shikijaku/MSc-MIDI-Controller/pictures/IMG_9758.JPG

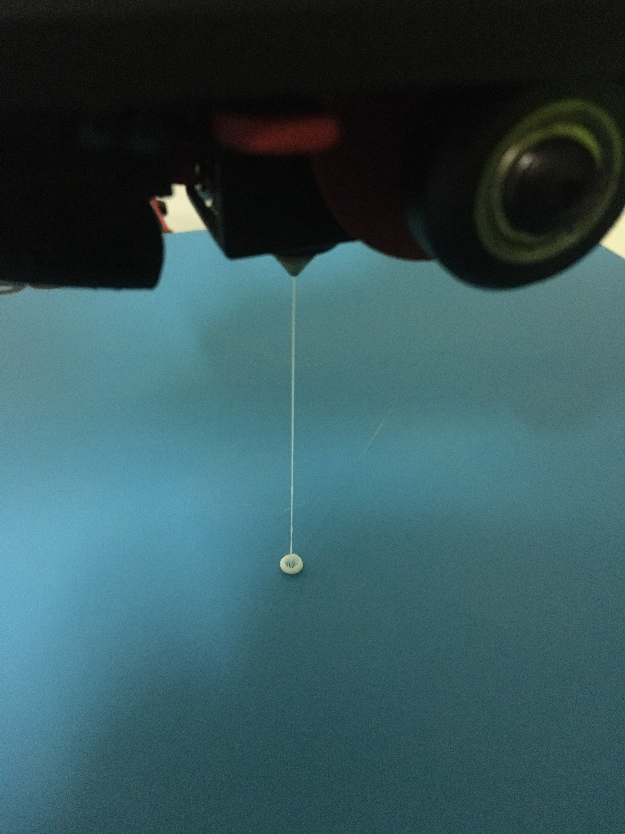
pictures/IMG_9758.JPG
