shikijaku/MSc-MIDI-Controller/pictures/IMG_9778.JPG

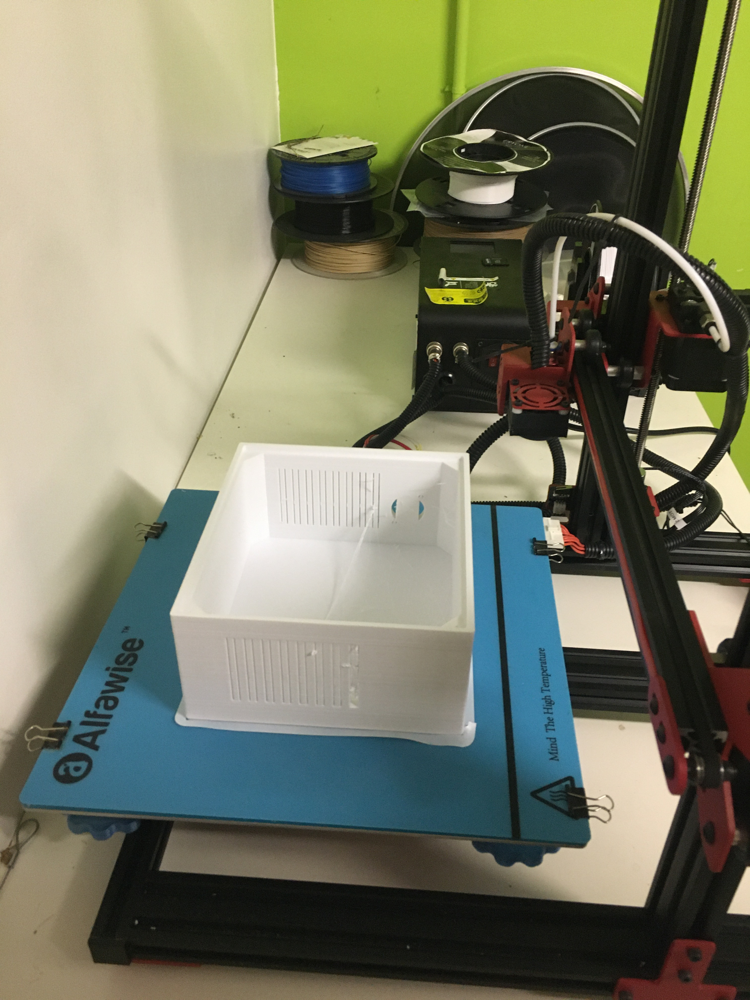
pictures/IMG_9778.JPG
