shikijaku/MSc-MIDI-Controller/pictures/IMG_9788.JPG

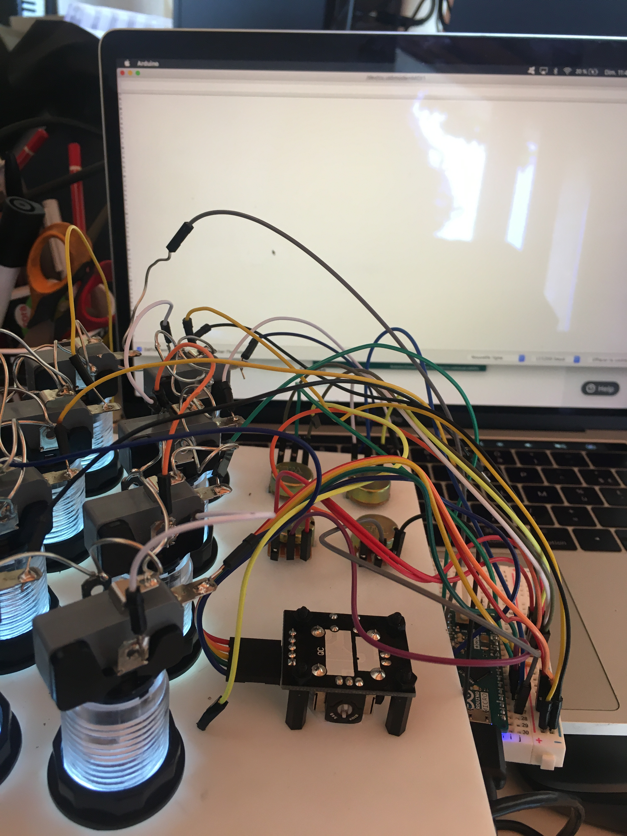
pictures/IMG_9788.JPG
