shikijaku/MSc-MIDI-Controller/pictures/IMG_9793.JPG

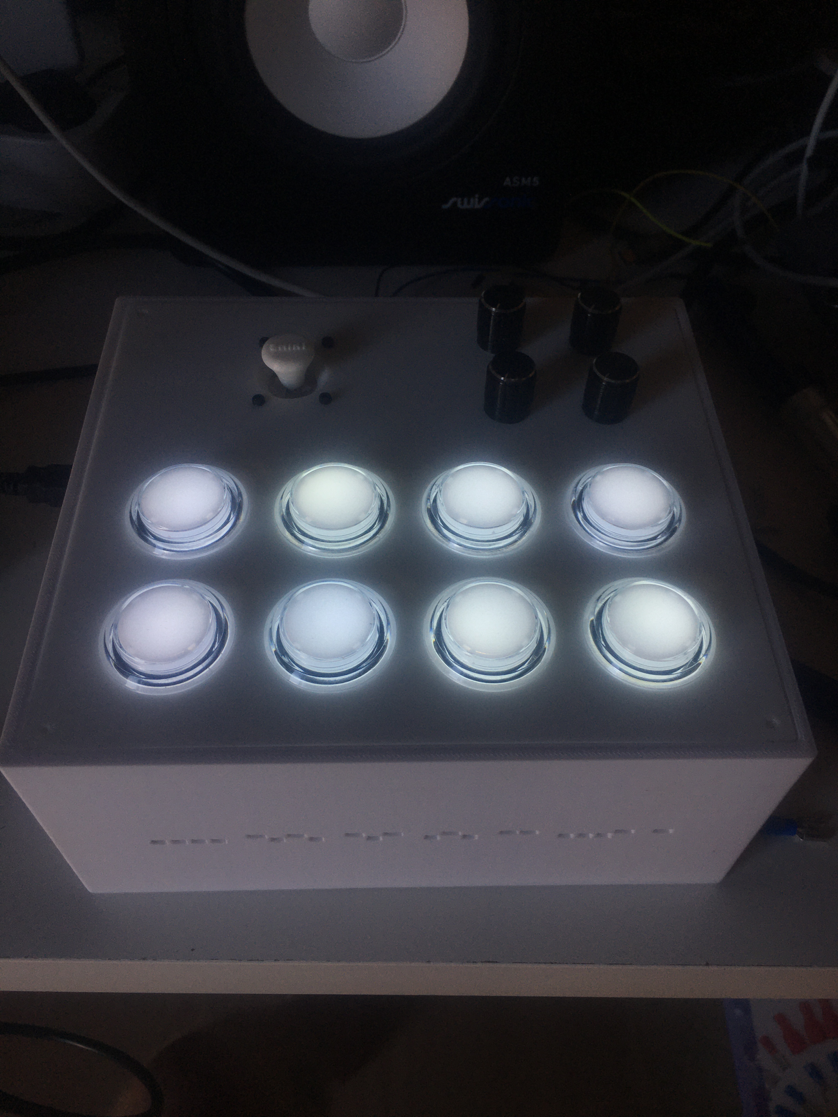
pictures/IMG_9793.JPG
