shikijaku/MSc-MIDI-Controller/pictures/IMG_9798.JPG

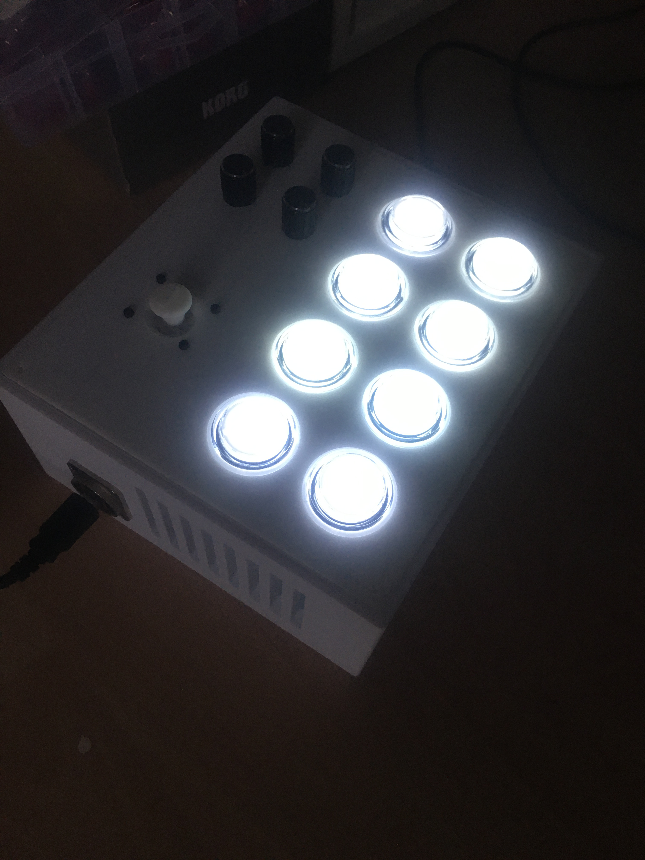
pictures/IMG_9798.JPG
