shikijaku/MSc-MIDI-Controller/pictures/IMG_9799.JPG

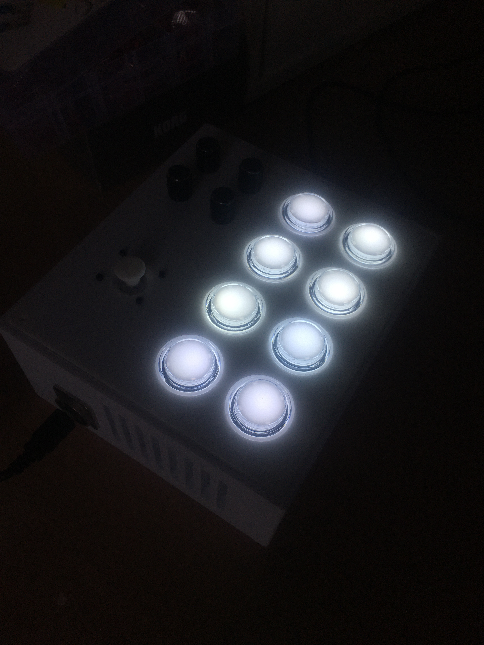
pictures/IMG_9799.JPG
