shikijaku/MSc-MIDI-Controller/pictures/IMG_9800.JPG

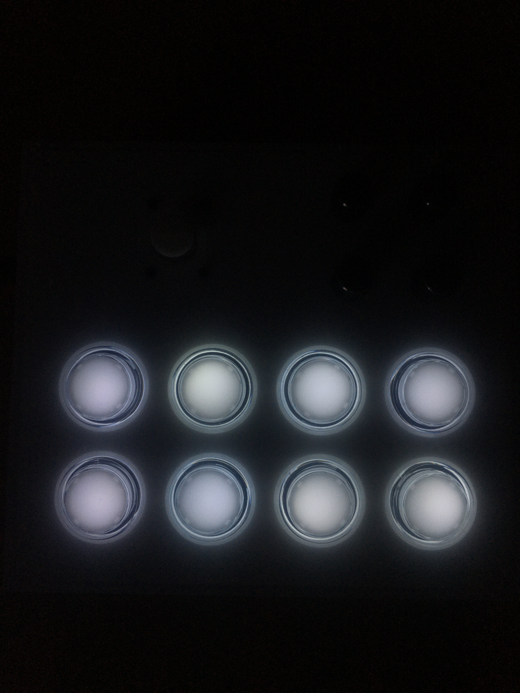
pictures/IMG_9800.JPG
