shikijaku/MSc-MIDI-Controller/pictures/IMG_9803.JPG

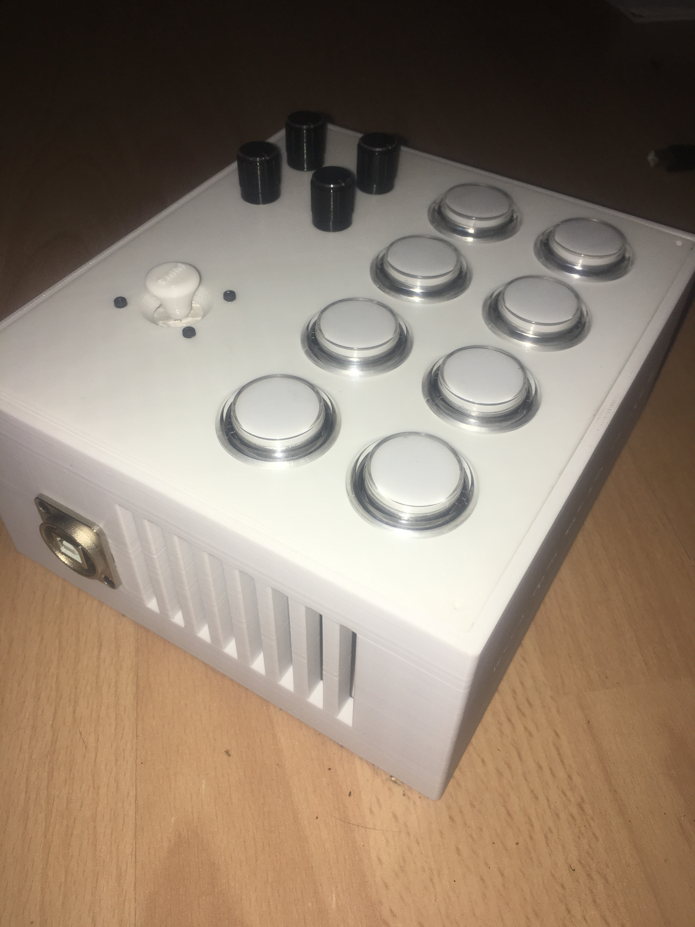
pictures/IMG_9803.JPG
