shikijaku/MSc-MIDI-Controller/pictures/IMG_9804.JPG

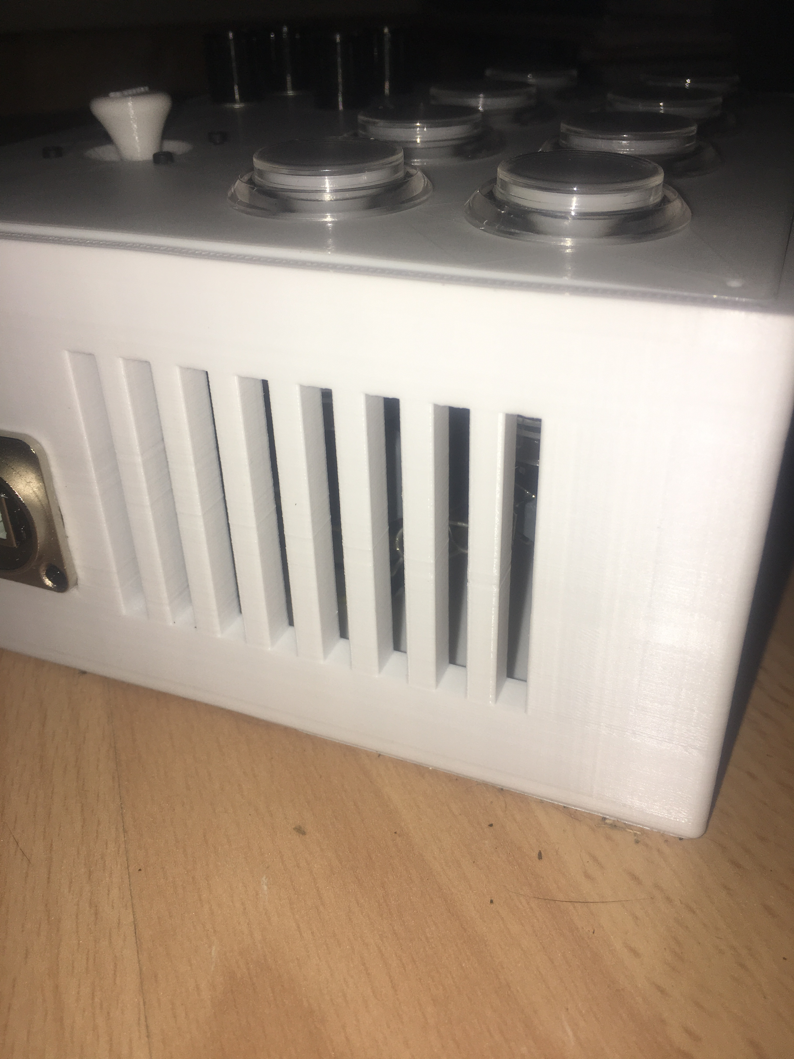
pictures/IMG_9804.JPG
