shikijaku/MSc-MIDI-Controller/pictures/IMG_9808.JPG

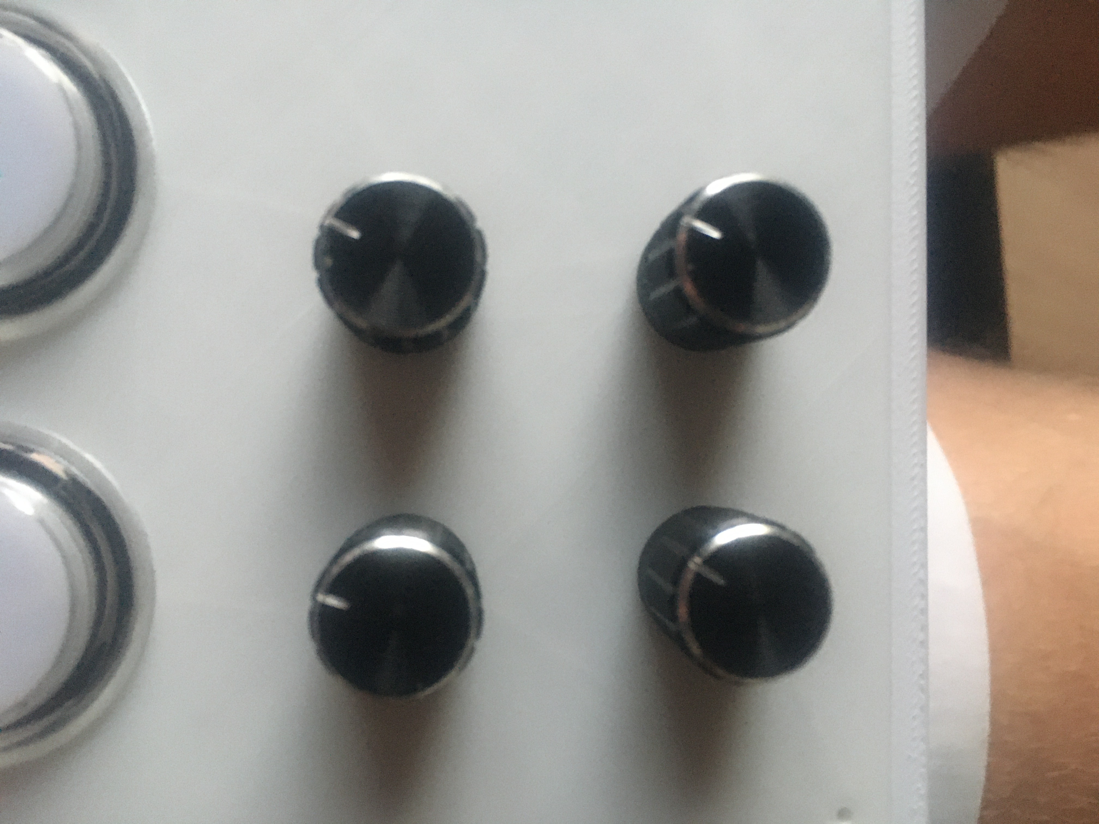
pictures/IMG_9808.JPG
