shikijaku/MSc-MIDI-Controller/pictures/IMG_9811.JPG

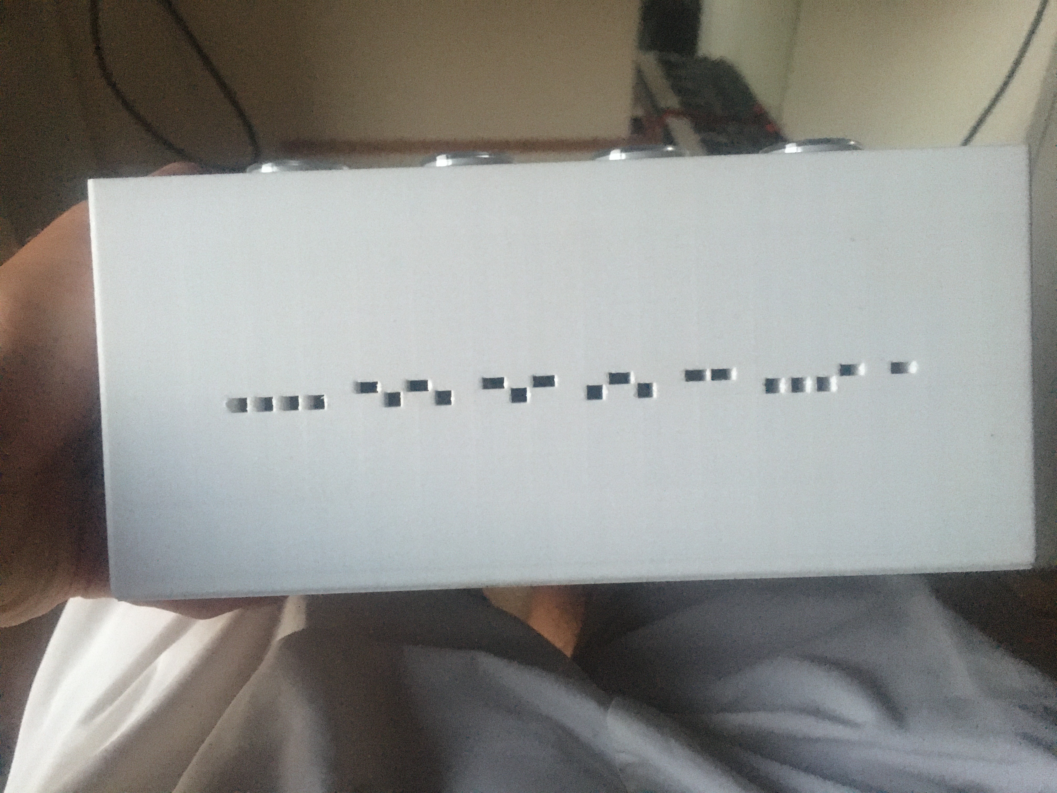
pictures/IMG_9811.JPG
