shikijaku/MSc-MIDI-Controller/pictures/IMG_9812.JPG

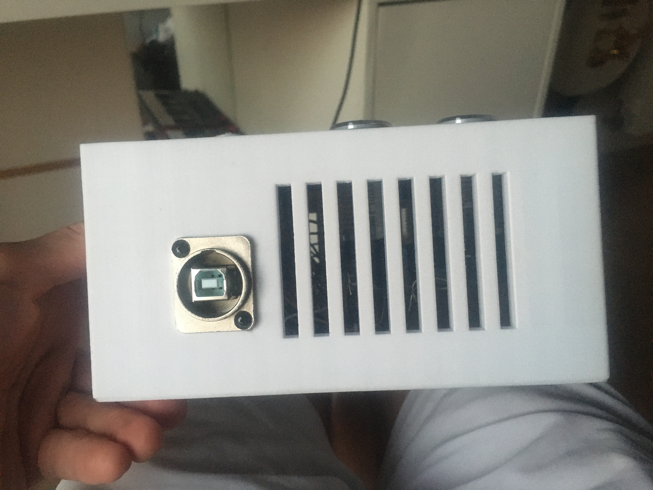
pictures/IMG_9812.JPG
