shikijaku/MSc-MIDI-Controller/pictures/IMG_9833.JPG

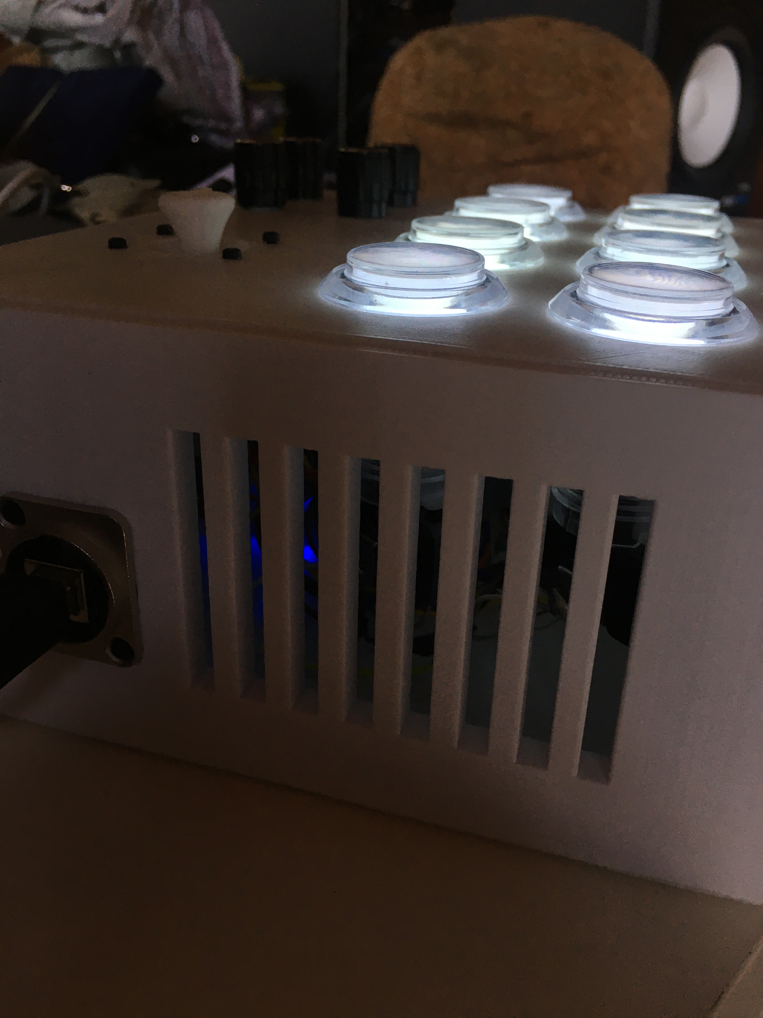
pictures/IMG_9833.JPG
