shikijaku/MSc-MIDI-Controller/pictures/IMG_9836.JPG

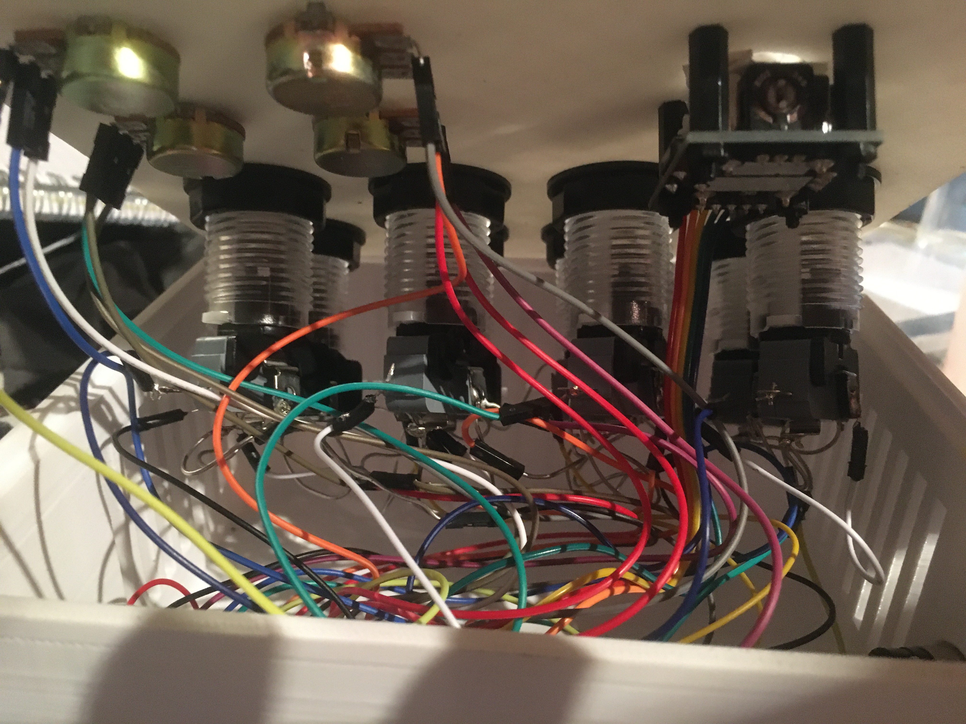
pictures/IMG_9836.JPG
