shikijaku/MSc-MIDI-Controller/pictures/IMG_9764.JPG

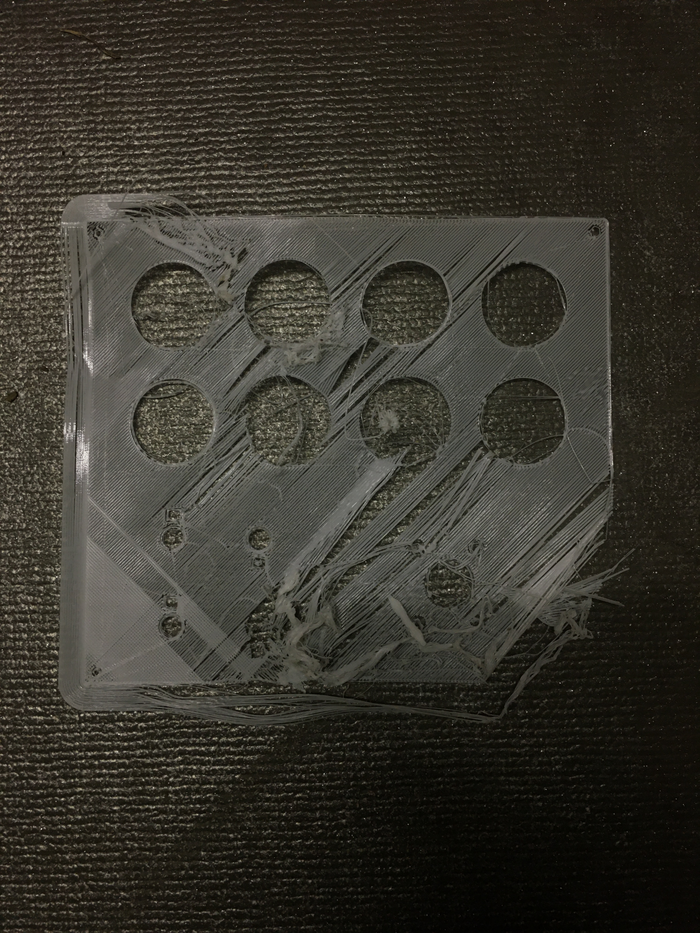
pictures/IMG_9764.JPG
