shikijaku/MSc-MIDI-Controller/pictures/IMG_9794.JPG

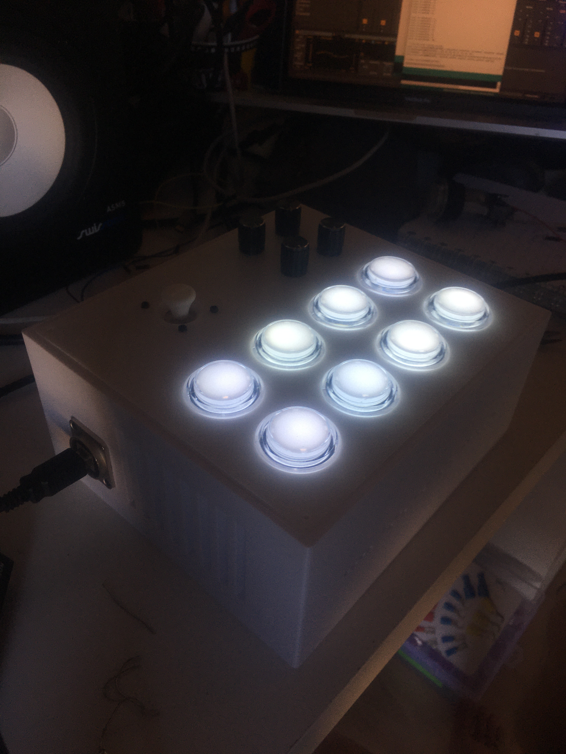
pictures/IMG_9794.JPG
