shikijaku/MSc-MIDI-Controller/pictures/IMG_9797.JPG

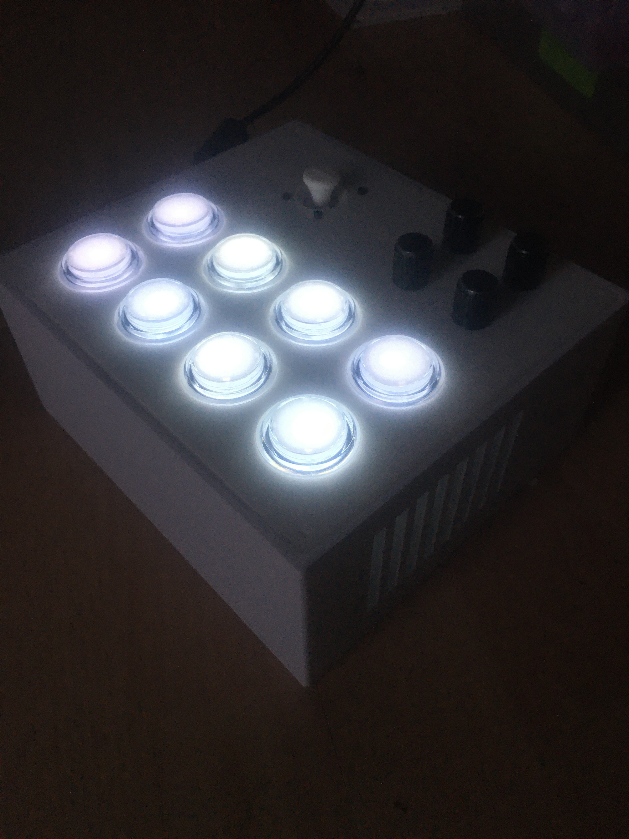
pictures/IMG_9797.JPG
