shikijaku/MSc-MIDI-Controller/pictures/IMG_9802.JPG

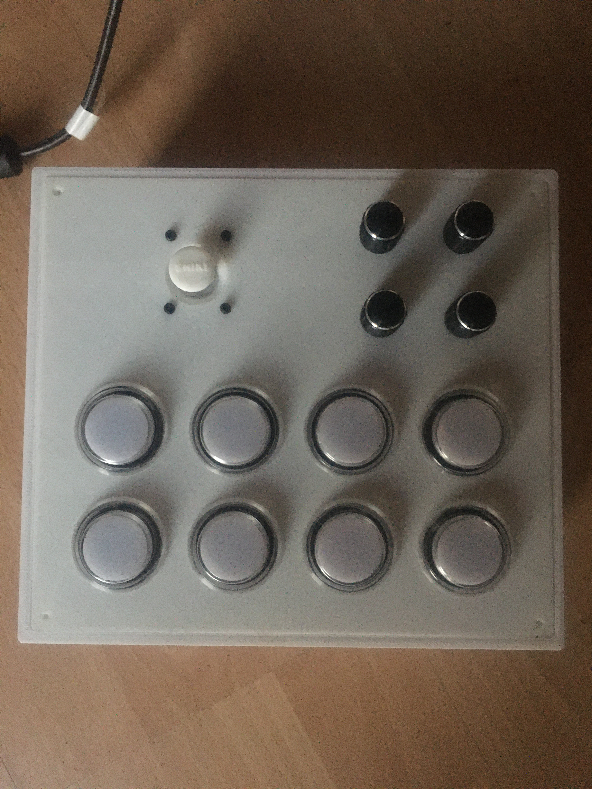
pictures/IMG_9802.JPG
