shikijaku/MSc-MIDI-Controller/pictures/IMG_9806.JPG

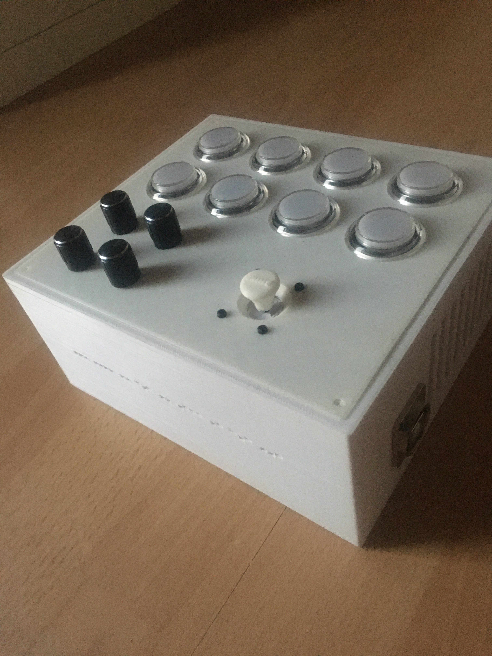
pictures/IMG_9806.JPG
