shikijaku/MSc-MIDI-Controller/pictures/IMG_9807.JPG

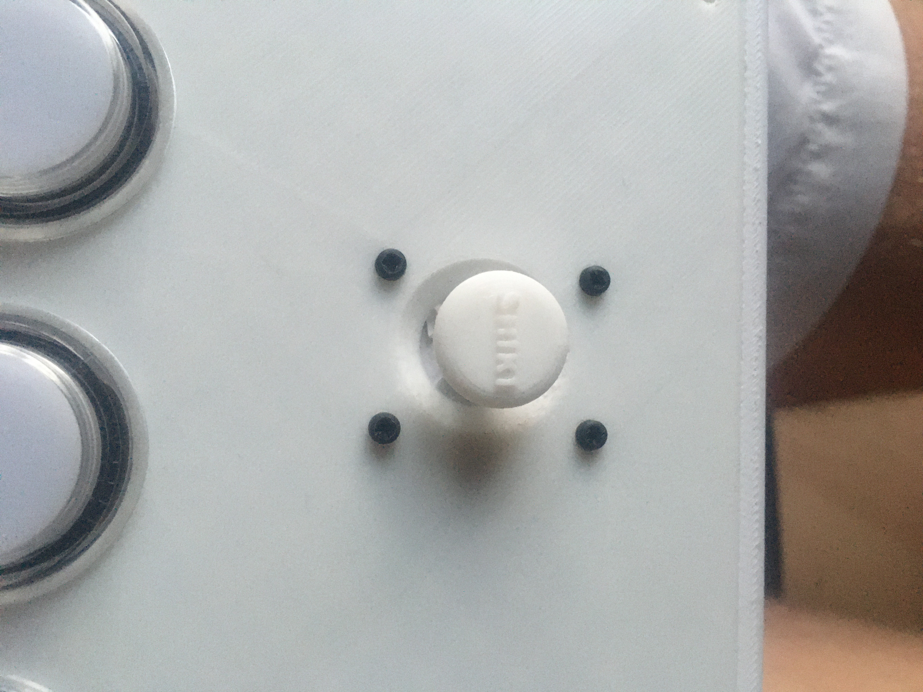
pictures/IMG_9807.JPG
