shikijaku/MSc-MIDI-Controller/pictures/IMG_9810.JPG

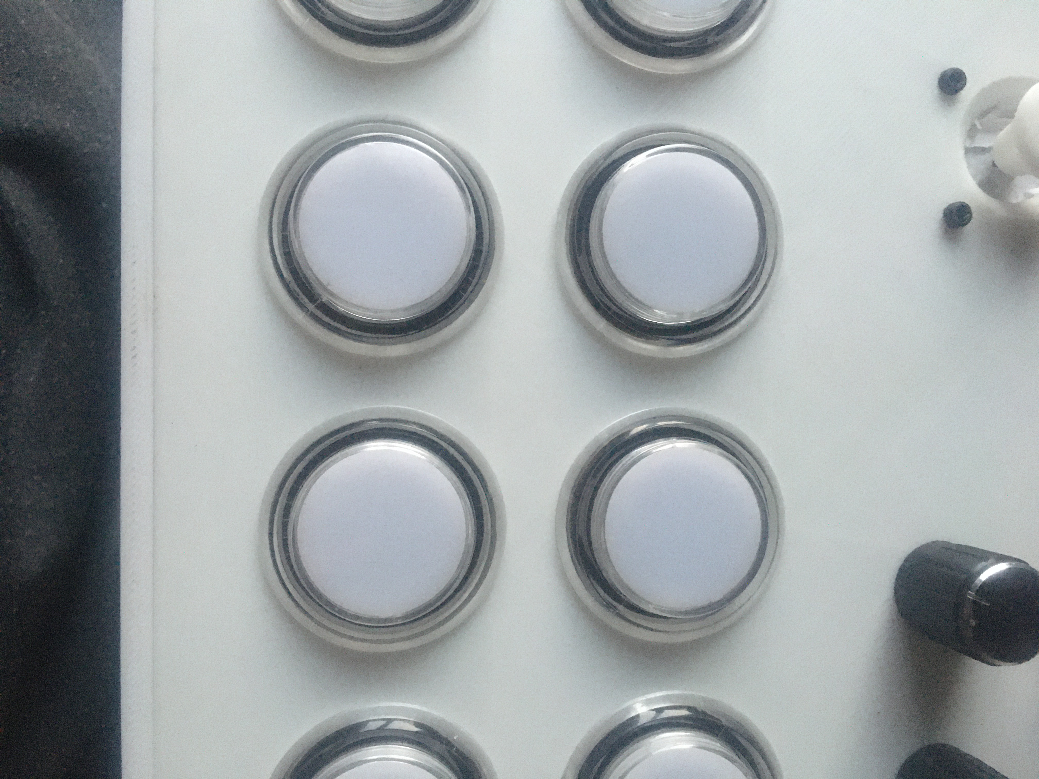
pictures/IMG_9810.JPG
